julbouln/musicboard/firmware/src/bsp/musicboard/musicboard.c

/**
  ******************************************************************************
  * @file    stm32746g_discovery.c
  * @author  MCD Application Team
  * @version V1.0.0
  * @date    25-June-2015
  * @brief   This file provides a set of firmware functions to manage LEDs, 
  *          push-buttons and COM ports available on STM32746G-Discovery
  *          board(MB1191) from STMicroelectronics.
  ******************************************************************************
  * @attention
  *
  * <h2><center>&copy; COPYRIGHT(c) 2015 STMicroelectronics</center></h2>
  *
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
  ******************************************************************************
  */ 

/* Includes ------------------------------------------------------------------*/
#include "musicboard.h"

/** @addtogroup BSP
  * @{
  */ 

/** @addtogroup STM32746G_DISCOVERY
  * @{
  */

/** @defgroup STM32746G_DISCOVERY_LOW_LEVEL STM32746G_DISCOVERY_LOW_LEVEL
  * @{
  */

/** @defgroup STM32746G_DISCOVERY_LOW_LEVEL_Private_TypesDefinitions STM32746G_DISCOVERY_LOW_LEVEL Private Types Definitions
  * @{
  */
/**
  * @}
  */

/** @defgroup STM32746G_DISCOVERY_LOW_LEVEL_Private_Defines STM32746G_DISCOVERY_LOW_LEVEL Private Defines
  * @{
  */
/**
 * @brief STM32746G DISCOVERY BSP Driver version number V1.0.0
   */
#define __STM32746G_DISCO_BSP_VERSION_MAIN   (0x01) /*!< [31:24] main version */
#define __STM32746G_DISCO_BSP_VERSION_SUB1   (0x00) /*!< [23:16] sub1 version */
#define __STM32746G_DISCO_BSP_VERSION_SUB2   (0x00) /*!< [15:8]  sub2 version */
#define __STM32746G_DISCO_BSP_VERSION_RC     (0x00) /*!< [7:0]  release candidate */
#define __STM32746G_DISCO_BSP_VERSION         ((__STM32746G_DISCO_BSP_VERSION_MAIN << 24)\
                                             |(__STM32746G_DISCO_BSP_VERSION_SUB1 << 16)\
                                             |(__STM32746G_DISCO_BSP_VERSION_SUB2 << 8 )\
                                             |(__STM32746G_DISCO_BSP_VERSION_RC))
/**
  * @}
  */

/** @defgroup STM32746G_DISCOVERY_LOW_LEVEL_Private_Macros STM32746G_DISCOVERY_LOW_LEVEL Private Macros
  * @{
  */
/**
  * @}
  */

/** @defgroup STM32746G_DISCOVERY_LOW_LEVEL_Private_Variables STM32746G_DISCOVERY_LOW_LEVEL Private Variables
  * @{
  */

#ifdef LED2_PIN
const uint32_t GPIO_PIN[LEDn] = {LED1_PIN, LED2_PIN};
const GPIO_TypeDef* GPIO_PORT[LEDn] = {LED1_GPIO_PORT, LED2_GPIO_PORT};
#else
const uint32_t GPIO_PIN[LEDn] = {LED1_PIN};
const GPIO_TypeDef* GPIO_PORT[LEDn] = {LED1_GPIO_PORT};
#endif
USART_TypeDef* COM_USART[COMn] = {MIDI_COM1};
GPIO_TypeDef* COM_TX_PORT[COMn] = {MIDI_COM1_TX_GPIO_PORT};
GPIO_TypeDef* COM_RX_PORT[COMn] = {MIDI_COM1_RX_GPIO_PORT};
const uint16_t COM_TX_PIN[COMn] = {MIDI_COM1_TX_PIN};
const uint16_t COM_RX_PIN[COMn] = {MIDI_COM1_RX_PIN};
const uint16_t COM_TX_AF[COMn] = {MIDI_COM1_TX_AF};
const uint16_t COM_RX_AF[COMn] = {MIDI_COM1_RX_AF};

static I2C_HandleTypeDef hI2cAudioHandler = {0};

/**
  * @}
  */

/** @defgroup STM32746G_DISCOVERY_LOW_LEVEL_Private_FunctionPrototypes STM32746G_DISCOVERY_LOW_LEVEL Private Function Prototypes
  * @{
  */
static void     I2Cx_MspInit(I2C_HandleTypeDef *i2c_handler);
static void     I2Cx_Init(I2C_HandleTypeDef *i2c_handler);

/* AUDIO IO functions */
void            AUDIO_IO_Init(void);
void            AUDIO_IO_DeInit(void);
void            AUDIO_IO_Write(uint8_t Addr, uint16_t Reg, uint16_t Value);
uint16_t        AUDIO_IO_Read(uint8_t Addr, uint16_t Reg);
void            AUDIO_IO_Delay(uint32_t Delay);

/** @defgroup STM32746G_DISCOVERY_LOW_LEVEL_Exported_Functions STM32746G_DISCOVERY_LOW_LEVELSTM32746G_DISCOVERY_LOW_LEVEL Exported Functions
  * @{
  */ 

  /**
  * @brief  This method returns the STM32746G DISCOVERY BSP Driver revision
  * @retval version: 0xXYZR (8bits for each decimal, R for RC)
  */
uint32_t BSP_GetVersion(void)
{
  return __STM32746G_DISCO_BSP_VERSION;
}

/**
  * @brief  Configures LED on GPIO.
  * @param  Led: LED to be configured.
  *          This parameter can be one of the following values:
  *            @arg  LED1
  * @retval None
  */
void BSP_LED_Init(Led_TypeDef Led)
{
  GPIO_InitTypeDef  gpio_init_structure;
  GPIO_TypeDef*     gpio_led;

  gpio_led = GPIO_PORT[Led];
  /* Enable the GPIO_LED clock */
  if (Led == LED1)
  {
    LED1_GPIO_CLK_ENABLE();
  }
#ifdef LED2_PIN
  if (Led == LED2)
  {
    LED2_GPIO_CLK_ENABLE();
  }
#endif
  /* Configure the GPIO_LED pin */
  gpio_init_structure.Pin = GPIO_PIN[Led];
  gpio_init_structure.Mode = GPIO_MODE_OUTPUT_PP;
  gpio_init_structure.Pull = GPIO_PULLUP;
  gpio_init_structure.Speed = GPIO_SPEED_HIGH;

  HAL_GPIO_Init(gpio_led, &gpio_init_structure);

  /* By default, turn off LED */
  HAL_GPIO_WritePin(gpio_led, GPIO_PIN[Led], GPIO_PIN_RESET);
}

/**
  * @brief  DeInit LEDs.
  * @param  Led: LED to be configured.
  *          This parameter can be one of the following values:
  *            @arg  LED1
  * @note Led DeInit does not disable the GPIO clock
  * @retval None
  */
void BSP_LED_DeInit(Led_TypeDef Led)
{
  GPIO_InitTypeDef  gpio_init_structure;
  GPIO_TypeDef*     gpio_led;

  gpio_led = GPIO_PORT[Led];
  /* Turn off LED */
  HAL_GPIO_WritePin(gpio_led, GPIO_PIN[Led], GPIO_PIN_RESET);
  /* Configure the GPIO_LED pin */
  gpio_init_structure.Pin = GPIO_PIN[Led];
  HAL_GPIO_DeInit(gpio_led, gpio_init_structure.Pin);
}

/**
  * @brief  Turns selected LED On.
  * @param  Led: LED to be set on
  *          This parameter can be one of the following values:
  *            @arg  LED1
  * @retval None
  */
void BSP_LED_On(Led_TypeDef Led)
{
  GPIO_TypeDef*     gpio_led;

  gpio_led = GPIO_PORT[Led];
  HAL_GPIO_WritePin(gpio_led, GPIO_PIN[Led], GPIO_PIN_SET);
}

/**
  * @brief  Turns selected LED Off.
  * @param  Led: LED to be set off
  *          This parameter can be one of the following values:
  *            @arg  LED1
  * @retval None
  */
void BSP_LED_Off(Led_TypeDef Led)
{
  GPIO_TypeDef*     gpio_led;

  gpio_led = GPIO_PORT[Led];
  HAL_GPIO_WritePin(gpio_led, GPIO_PIN[Led], GPIO_PIN_RESET);
}

/**
  * @brief  Toggles the selected LED.
  * @param  Led: LED to be toggled
  *          This parameter can be one of the following values:
  *            @arg  LED1
  * @retval None
  */
void BSP_LED_Toggle(Led_TypeDef Led)
{
  GPIO_TypeDef*     gpio_led;

  gpio_led = GPIO_PORT[Led];
  HAL_GPIO_TogglePin(gpio_led, GPIO_PIN[Led]);
}

/**
  * @brief  Configures COM port.
  * @param  COM: COM port to be configured.
  *          This parameter can be one of the following values:
  *            @arg  COM1 
  *            @arg  COM2 
  * @param  huart: Pointer to a UART_HandleTypeDef structure that contains the
  *                configuration information for the specified USART peripheral.
  * @retval None
  */
void BSP_COM_Init(COM_TypeDef COM, UART_HandleTypeDef *huart)
{
  GPIO_InitTypeDef gpio_init_structure;

  /* Enable GPIO clock */
  MIDI_COMx_TX_GPIO_CLK_ENABLE(COM);
  MIDI_COMx_RX_GPIO_CLK_ENABLE(COM);

  /* Enable USART clock */
  MIDI_COMx_CLK_ENABLE(COM);

  /* Configure USART Tx as alternate function */
  gpio_init_structure.Pin = COM_TX_PIN[COM];
  gpio_init_structure.Mode = GPIO_MODE_AF_PP;
  gpio_init_structure.Speed = GPIO_SPEED_FAST;
  gpio_init_structure.Pull = GPIO_PULLUP;
  gpio_init_structure.Alternate = COM_TX_AF[COM];
  HAL_GPIO_Init(COM_TX_PORT[COM], &gpio_init_structure);

  /* Configure USART Rx as alternate function */
  gpio_init_structure.Pin = COM_RX_PIN[COM];
  gpio_init_structure.Mode = GPIO_MODE_AF_PP;
  gpio_init_structure.Alternate = COM_RX_AF[COM];
  HAL_GPIO_Init(COM_RX_PORT[COM], &gpio_init_structure);

  /* USART configuration */
  huart->Instance = COM_USART[COM];

  huart->Init.BaudRate = 31250;
  huart->Init.WordLength = UART_WORDLENGTH_8B;
  huart->Init.StopBits = UART_STOPBITS_1;
  huart->Init.Parity = UART_PARITY_NONE;
  huart->Init.Mode = UART_MODE_TX_RX;
  huart->Init.HwFlowCtl = UART_HWCONTROL_NONE;
  huart->Init.OverSampling = UART_OVERSAMPLING_16;
  huart->Init.OneBitSampling = UART_ONE_BIT_SAMPLE_DISABLE;
  huart->AdvancedInit.AdvFeatureInit = UART_ADVFEATURE_NO_INIT;

  HAL_UART_Init(huart);
}

/**
  * @brief  DeInit COM port.
  * @param  COM: COM port to be configured.
  *          This parameter can be one of the following values:
  *            @arg  COM1 
  *            @arg  COM2 
  * @param  huart: Pointer to a UART_HandleTypeDef structure that contains the
  *                configuration information for the specified USART peripheral.
  * @retval None
  */
void BSP_COM_DeInit(COM_TypeDef COM, UART_HandleTypeDef *huart)
{
  /* USART configuration */
  huart->Instance = COM_USART[COM];
  HAL_UART_DeInit(huart);

  /* Enable USART clock */
  MIDI_COMx_CLK_DISABLE(COM);

  /* DeInit GPIO pins can be done in the application 
     (by surcharging this __weak function) */

  /* GPIO pins clock, DMA clock can be shut down in the application 
     by surcharging this __weak function */
}

/*******************************************************************************
                            BUS OPERATIONS
*******************************************************************************/

/******************************* I2C Routines *********************************/
/**
  * @brief  Initializes I2C MSP.
  * @param  i2c_handler : I2C handler
  * @retval None
  */
static void I2Cx_MspInit(I2C_HandleTypeDef *i2c_handler)
{
  GPIO_InitTypeDef  gpio_init_structure;
  
  if (i2c_handler == (I2C_HandleTypeDef*)(&hI2cAudioHandler))
  {
    /* AUDIO MSP init */

    /* rev0 bug, set PB10 as input */
    gpio_init_structure.Pin = GPIO_PIN_10;
    gpio_init_structure.Mode = GPIO_MODE_INPUT;
    gpio_init_structure.Pull = GPIO_NOPULL;
    gpio_init_structure.Speed = GPIO_SPEED_FAST;
    HAL_GPIO_Init(GPIOB, &gpio_init_structure);

    /*** Configure the GPIOs ***/
    /* Enable GPIO clock */
    DISCOVERY_AUDIO_I2Cx_SCL_SDA_GPIO_CLK_ENABLE();

    /* Configure I2C Tx as alternate function */
    gpio_init_structure.Pin = DISCOVERY_AUDIO_I2Cx_SCL_PIN;
    gpio_init_structure.Mode = GPIO_MODE_AF_OD;
    gpio_init_structure.Pull = GPIO_NOPULL;
    gpio_init_structure.Speed = GPIO_SPEED_FAST;
    gpio_init_structure.Alternate = DISCOVERY_AUDIO_I2Cx_SCL_SDA_AF;
    HAL_GPIO_Init(DISCOVERY_AUDIO_I2Cx_SCL_SDA_GPIO_PORT, &gpio_init_structure);

    /* Configure I2C Rx as alternate function */
    gpio_init_structure.Pin = DISCOVERY_AUDIO_I2Cx_SDA_PIN;
    HAL_GPIO_Init(DISCOVERY_AUDIO_I2Cx_SCL_SDA_GPIO_PORT, &gpio_init_structure);

    /*** Configure the I2C peripheral ***/
    /* Enable I2C clock */
    DISCOVERY_AUDIO_I2Cx_CLK_ENABLE();

    /* Force the I2C peripheral clock reset */
    DISCOVERY_AUDIO_I2Cx_FORCE_RESET();

    /* Release the I2C peripheral clock reset */
    DISCOVERY_AUDIO_I2Cx_RELEASE_RESET();

    /* Enable and set I2Cx Interrupt to a lower priority */
    HAL_NVIC_SetPriority(DISCOVERY_AUDIO_I2Cx_EV_IRQn, 0x05, 0);
    HAL_NVIC_EnableIRQ(DISCOVERY_AUDIO_I2Cx_EV_IRQn);

    /* Enable and set I2Cx Interrupt to a lower priority */
    HAL_NVIC_SetPriority(DISCOVERY_AUDIO_I2Cx_ER_IRQn, 0x05, 0);
    HAL_NVIC_EnableIRQ(DISCOVERY_AUDIO_I2Cx_ER_IRQn);
  }
}

/**
  * @brief  Initializes I2C HAL.
  * @param  i2c_handler : I2C handler
  * @retval None
  */
static void I2Cx_Init(I2C_HandleTypeDef *i2c_handler)
{
  if(HAL_I2C_GetState(i2c_handler) == HAL_I2C_STATE_RESET)
  {
    if (i2c_handler == (I2C_HandleTypeDef*)(&hI2cAudioHandler))
    {
      /* Audio and LCD I2C configuration */
      i2c_handler->Instance = DISCOVERY_AUDIO_I2Cx;
    }

    i2c_handler->Init.Timing           = 0x10E66A8D; // generated by cubemx
    i2c_handler->Init.OwnAddress1      = 0;
    i2c_handler->Init.AddressingMode   = I2C_ADDRESSINGMODE_7BIT;
    i2c_handler->Init.DualAddressMode  = I2C_DUALADDRESS_DISABLE;
    i2c_handler->Init.OwnAddress2      = 0;
    i2c_handler->Init.GeneralCallMode  = I2C_GENERALCALL_DISABLE;
    i2c_handler->Init.NoStretchMode    = I2C_NOSTRETCH_DISABLE;

    /* Init the I2C */
    I2Cx_MspInit(i2c_handler);
    HAL_I2C_Init(i2c_handler);
  }
}

/*******************************************************************************
                            LINK OPERATIONS
*******************************************************************************/

/********************************* LINK AUDIO *********************************/

/**
  * @brief  Initializes Audio low level.
  * @retval None
  */
void AUDIO_IO_Init(void) 
{
  I2Cx_Init(&hI2cAudioHandler);
  //I2Cx_IsDeviceReady(&hI2cAudioHandler,AUDIO_I2C_ADDRESS,10);

}

/**
  * @brief  Deinitializes Audio low level.
  * @retval None
  */
void AUDIO_IO_DeInit(void)
{
}

/**
  * @brief  Writes a single data.
  * @param  Addr: I2C address
  * @param  Reg: Reg address 
  * @param  Value: Data to be written
  * @retval None
  */
void AUDIO_IO_Write(uint8_t Addr, uint16_t Reg, uint16_t Value)
{
  uint8_t cmd[2];
  /* Assemble 2-byte data in WM8731 format */
  cmd[0] = ((Reg << 1) & 0xFE) | ((Value >> 8) & 0x01);
  cmd[1] = Value & 0xFF;

  HAL_I2C_Master_Transmit(&hI2cAudioHandler, Addr, cmd, 2, 2000);  
}

/**
  * @brief  Reads a single data.
  * @param  Addr: I2C address
  * @param  Reg: Reg address 
  * @retval Data to be read
  */
uint16_t AUDIO_IO_Read(uint8_t Addr, uint16_t Reg)
{
  uint16_t read_value = 0;
  HAL_I2C_Master_Receive(&hI2cAudioHandler, Addr, (uint8_t*)&read_value, 2, 100);
  return read_value;
}

/**
  * @brief  AUDIO Codec delay 
  * @param  Delay: Delay in ms
  * @retval None
  */
void AUDIO_IO_Delay(uint32_t Delay)
{
  HAL_Delay(Delay);
}
