julbouln/musicboard/firmware/src/efluidsynth/fluid_voice.c

#include "fluid_voice.h"
#include "fluid_mod.h"
#include "fluid_chan.h"
#include "fluid_conv.h"
#include "fluid_synth.h"
#include "fluid_sys.h"
#include "fluid_sfont.h"
#include "fluid_log.h"

#include "fluid_types.h"

/* used for filter turn off optimization - if filter cutoff is above the
   specified value and filter q is below the other value, turn filter off */
#define FLUID_MAX_AUDIBLE_FILTER_FC 19000.0f
#define FLUID_MIN_AUDIBLE_FILTER_Q 1.2f

/* Smallest amplitude that can be perceived (full scale is +/- 0.5)
 * 16 bits => 96+4=100 dB dynamic range => 0.00001
 * 0.00001 * 2 is approximately 0.00003 :)
 */
#define FLUID_NOISE_FLOOR 0.00003

/* these should be the absolute minimum that FluidSynth can deal with */
#define FLUID_MIN_LOOP_SIZE 2
#define FLUID_MIN_LOOP_PAD 0

/* min vol envelope release (to stop clicks) in SoundFont timecents */
#define FLUID_MIN_VOLENVRELEASE -7200.0f /* ~16ms */

/*
 * new_fluid_voice
 */
fluid_voice_t*
new_fluid_voice(fluid_real_t output_rate)
{
  fluid_voice_t* voice;
  voice = FLUID_NEW(fluid_voice_t);
  if (voice == NULL) {
    FLUID_LOG(FLUID_ERR, "Out of memory");
    return NULL;
  }
  voice->status = FLUID_VOICE_CLEAN;
  voice->chan = NO_CHANNEL;
  voice->key = 0;
  voice->vel = 0;
  voice->channel = NULL;
  voice->sample = NULL;
  voice->output_rate = output_rate;

  /* The 'sustain' and 'finished' segments of the volume / modulation
   * envelope are constant. They are never affected by any modulator
   * or generator. Therefore it is enough to initialize them once
   * during the lifetime of the synth.
   */
  voice->volenv_data[FLUID_VOICE_ENVSUSTAIN].count = 0xffffffff;
  voice->volenv_data[FLUID_VOICE_ENVSUSTAIN].coeff = 1.0f;
  voice->volenv_data[FLUID_VOICE_ENVSUSTAIN].incr = 0.0f;
  voice->volenv_data[FLUID_VOICE_ENVSUSTAIN].min = -1.0f;
  voice->volenv_data[FLUID_VOICE_ENVSUSTAIN].max = 2.0f;

  voice->volenv_data[FLUID_VOICE_ENVFINISHED].count = 0xffffffff;
  voice->volenv_data[FLUID_VOICE_ENVFINISHED].coeff = 0.0f;
  voice->volenv_data[FLUID_VOICE_ENVFINISHED].incr = 0.0f;
  voice->volenv_data[FLUID_VOICE_ENVFINISHED].min = -1.0f;
  voice->volenv_data[FLUID_VOICE_ENVFINISHED].max = 1.0f;

  voice->modenv_data[FLUID_VOICE_ENVSUSTAIN].count = 0xffffffff;
  voice->modenv_data[FLUID_VOICE_ENVSUSTAIN].coeff = 1.0f;
  voice->modenv_data[FLUID_VOICE_ENVSUSTAIN].incr = 0.0f;
  voice->modenv_data[FLUID_VOICE_ENVSUSTAIN].min = -1.0f;
  voice->modenv_data[FLUID_VOICE_ENVSUSTAIN].max = 2.0f;

  voice->modenv_data[FLUID_VOICE_ENVFINISHED].count = 0xffffffff;
  voice->modenv_data[FLUID_VOICE_ENVFINISHED].coeff = 0.0f;
  voice->modenv_data[FLUID_VOICE_ENVFINISHED].incr = 0.0f;
  voice->modenv_data[FLUID_VOICE_ENVFINISHED].min = -1.0f;
  voice->modenv_data[FLUID_VOICE_ENVFINISHED].max = 1.0f;

  voice->gen = NULL;
  voice->mod = NULL;

  return voice;
}

int delete_fluid_voice(fluid_voice_t* voice)
{
  if (voice == NULL) {
    return FLUID_OK;
  }

  FLUID_FREE(voice);
  return FLUID_OK;
}

int fluid_voice_init(fluid_voice_t* voice, fluid_sample_t* sample,
                 fluid_channel_t* channel, int key, int vel, unsigned int id,
                 unsigned int start_time, fluid_real_t gain)
{
  /* Note: The voice parameters will be initialized later, when the
   * generators have been retrieved from the sound font. Here, only
   * the 'working memory' of the voice (position in envelopes, history
   * of IIR filters, position in sample etc) is initialized. */

  voice->id = id;
  voice->chan = fluid_channel_get_num(channel);
  voice->key = (uint8_t) key;
  voice->vel = (uint8_t) vel;
  voice->channel = channel;
  voice->mod_count = 0;
  voice->sample = sample;
  voice->start_time = start_time;
  voice->ticks = 0;
  voice->has_looped = 0; /* Will be set during voice_write when the 2nd loop point is reached */
  voice->last_fres = -1; /* The filter coefficients have to be calculated later in the DSP loop. */
  voice->filter_startup = 1; /* Set the filter immediately, don't fade between old and new settings */
  voice->interp_method = fluid_channel_get_interp_method(voice->channel);

  /* vol env initialization */
  voice->volenv_count = 0;
  voice->volenv_section = 0;
  voice->volenv_val = 0.0f;

#ifdef FLUID_FIXED_POINT
  voice->amp = 0;
#else
  voice->amp = 0.0f; /* The last value of the volume envelope, used to
                        calculate the volume increment during
                        processing */
#endif
  /* mod env initialization*/
  voice->modenv_count = 0;
  voice->modenv_section = 0;
  voice->modenv_val = 0.0f;

  voice->modlfo_val = 0.0;/* Fixme: Retrieve from any other existing
                             voice on this channel to keep LFOs in
                             unison? */

  voice->viblfo_val = 0.0f; /* Fixme: See mod lfo */

  /* Clear sample history in filter */
#ifdef FLUID_SIMPLE_IIR
  voice->vibrapos = 0;
  voice->vibraspeed = 0;
#else
  voice->hist1 = 0;
  voice->hist2 = 0;
#endif


  /* Set all the generators to their default value, according to SF
   * 2.01 section 8.1.3 (page 48). The value of NRPN messages are
   * copied from the channel to the voice's generators. The sound font
   * loader overwrites them. The generator values are later converted
   * into voice parameters in
   * fluid_voice_calculate_runtime_synthesis_parameters.  */
  fluid_list_t *pg;
  pg = voice->gen;
  while (pg != NULL) {
    fluid_gen_t *tmpgen = (fluid_gen_t *) pg->data;
    FLUID_FREE(tmpgen);
    pg->data = NULL;
    pg = fluid_list_next(pg);
  }
  delete_fluid_list(voice->gen);
  voice->gen = NULL;

  voice->synth_gain = gain;
  /* avoid division by zero later*/
  if (voice->synth_gain < 0.0000001) {
    voice->synth_gain = 0.0000001;
  }

  /* For a looped sample, this value will be overwritten as soon as the
   * loop parameters are initialized (they may depend on modulators).
   * This value can be kept, it is a worst-case estimate.
   */

  voice->amplitude_that_reaches_noise_floor_nonloop = FLUID_NOISE_FLOOR / voice->synth_gain;
  voice->amplitude_that_reaches_noise_floor_loop = FLUID_NOISE_FLOOR / voice->synth_gain;

  /* Increment the reference count of the sample to prevent the
     unloading of the soundfont while this voice is playing. */
  fluid_sample_incr_ref(voice->sample);

  fluid_list_t *p;
  p = voice->mod;
  while (p != NULL) {
    fluid_mod_t *tmpmod = (fluid_mod_t *) p->data;
    FLUID_FREE(tmpmod);
    p->data = NULL;
    p = fluid_list_next(p);
  }
  delete_fluid_list(voice->mod);
  voice->mod = NULL;

  return FLUID_OK;
}

extern fluid_gen_info_t fluid_gen_info[];

fluid_gen_t *fluid_voice_gen_get_or_add(fluid_voice_t *voice, uint8_t num) {
  fluid_gen_t *gen = fluid_gen_get(voice->gen, num);
  if (!gen) {
    gen = fluid_gen_create(num);
#ifndef FLUID_NO_NRPN_EXT
    gen->nrpn = fluid_channel_get_gen(voice->channel, num);
#endif
//        printf("%d %f\n",num,gen->nrpn);
    voice->gen = fluid_list_append(voice->gen, gen);
  }

  return gen;
}

fluid_real_t fluid_voice_gen_val_or_default(fluid_voice_t *voice, uint8_t num) {
  fluid_gen_t *gen = fluid_gen_get(voice->gen, num);
  if (gen)
    return gen->val;
  else
    return fluid_gen_info[num].def;
}

fluid_real_t fluid_voice_gen_val_all_or_default(fluid_voice_t *voice, uint8_t num) {
  fluid_gen_t *gen = fluid_gen_get(voice->gen, num);

#ifndef FLUID_NO_NRPN_EXT
  if (gen)
    return (gen->val + gen->mod + gen->nrpn);
  else
    return fluid_gen_info[num].def;
#else
  if (gen)
    return (gen->val + gen->mod);
  else
    return fluid_gen_info[num].def;
#endif
}

void fluid_voice_gen_set(fluid_voice_t* voice, int i, float val)
{
  fluid_gen_t *gen = fluid_voice_gen_get_or_add(voice, i);
  gen->val = val;
  gen->flags = GEN_SET;
}

void fluid_voice_gen_incr(fluid_voice_t* voice, int i, float val)
{
  fluid_gen_t *gen = fluid_voice_gen_get_or_add(voice, i);
  gen->val += val;
  gen->flags = GEN_SET;
}

float fluid_voice_gen_get(fluid_voice_t* voice, int num)
{
//  fluid_gen_t *gen = fluid_voice_gen_get_or_add(voice, num);
  return fluid_voice_gen_val_or_default(voice, num);
}

fluid_real_t fluid_voice_gen_value(fluid_voice_t* voice, int num)
{
  /* This is an extension to the SoundFont standard. More
   * documentation is available at the fluid_synth_set_gen2()
   * function. */

  fluid_gen_t *gen = fluid_voice_gen_get_or_add(voice, num);
#ifndef FLUID_NO_NRPN_EXT
  if (gen->flags == GEN_ABS_NRPN) {
    return gen->nrpn;

  } else {
    return (fluid_real_t) (gen->val + gen->mod + gen->nrpn);
  }
#else
  return (fluid_real_t) (gen->val + gen->mod);
#endif
}

int fluid_voice_calc_vol_mod_env(fluid_voice_t *voice) {
  fluid_env_data_t* env_data;
  fluid_real_t x;

  env_data = &voice->volenv_data[voice->volenv_section];

  /* skip to the next section of the envelope if necessary */
  while (voice->volenv_count >= env_data->count)
  {
    // If we're switching envelope stages from decay to sustain, force the value to be the end value of the previous stage
    if (env_data && voice->volenv_section == FLUID_VOICE_ENVDECAY)
      voice->volenv_val = env_data->min * env_data->coeff;

    env_data = &voice->volenv_data[++voice->volenv_section];
    voice->volenv_count = 0;
  }

  /* calculate the envelope value and check for valid range */
  x = env_data->coeff * voice->volenv_val + env_data->incr;
  if (x < env_data->min)
  {
    x = env_data->min;
    voice->volenv_section++;
    voice->volenv_count = 0;
  }
  else if (x > env_data->max)
  {
    x = env_data->max;
    voice->volenv_section++;
    voice->volenv_count = 0;
  }

  voice->volenv_val = x;
  voice->volenv_count++;

  if (voice->volenv_section == FLUID_VOICE_ENVFINISHED)
  {
    fluid_voice_off (voice);
    return 1;
  }

  env_data = &voice->modenv_data[voice->modenv_section];

  /* skip to the next section of the envelope if necessary */
  while (voice->modenv_count >= env_data->count)
  {
    env_data = &voice->modenv_data[++voice->modenv_section];
    voice->modenv_count = 0;
  }

  /* calculate the envelope value and check for valid range */
  x = env_data->coeff * voice->modenv_val + env_data->incr;

  if (x < env_data->min)
  {
    x = env_data->min;
    voice->modenv_section++;
    voice->modenv_count = 0;
  }
  else if (x > env_data->max)
  {
    x = env_data->max;
    voice->modenv_section++;
    voice->modenv_count = 0;
  }

  voice->modenv_val = x;
  voice->modenv_count++;
  return 0;
}

int fluid_voice_calc_lfo(fluid_voice_t *voice) {
  if (voice->ticks >= voice->modlfo_delay)
  {
    voice->modlfo_val += voice->modlfo_incr;

    if (voice->modlfo_val > 1.0)
    {
      voice->modlfo_incr = -voice->modlfo_incr;
      voice->modlfo_val = (fluid_real_t) 2.0 - voice->modlfo_val;
    }
    else if (voice->modlfo_val < -1.0)
    {
      voice->modlfo_incr = -voice->modlfo_incr;
      voice->modlfo_val = (fluid_real_t) - 2.0 - voice->modlfo_val;
    }
  }

  if (voice->ticks >= voice->viblfo_delay)
  {
    voice->viblfo_val += voice->viblfo_incr;

    if (voice->viblfo_val > (fluid_real_t) 1.0)
    {
      voice->viblfo_incr = -voice->viblfo_incr;
      voice->viblfo_val = (fluid_real_t) 2.0 - voice->viblfo_val;
    }
    else if (voice->viblfo_val < -1.0)
    {
      voice->viblfo_incr = -voice->viblfo_incr;
      voice->viblfo_val = (fluid_real_t) - 2.0 - voice->viblfo_val;
    }
  }
  return 0;
}

int fluid_voice_calc_amp(fluid_voice_t *voice) {
  fluid_real_t target_amp;

  if (voice->volenv_section == FLUID_VOICE_ENVDELAY)
    return 1;  /* The volume amplitude is in hold phase. No sound is produced. */

  if (voice->volenv_section == FLUID_VOICE_ENVATTACK)
  {
    /* the envelope is in the attack section: ramp linearly to max value.
     * A positive modlfo_to_vol should increase volume (negative attenuation).
     */
    target_amp = fluid_atten2amp (voice->attenuation)
                 * fluid_cb2amp (voice->modlfo_val * -voice->modlfo_to_vol)
                 * voice->volenv_val;
  }
  else
  {
    fluid_real_t amplitude_that_reaches_noise_floor;
    fluid_real_t amp_max;

    target_amp = fluid_atten2amp (voice->attenuation) * fluid_cb2amp (960.0f * (1.0f - voice->volenv_val) + voice->modlfo_val * -voice->modlfo_to_vol);

    /* We turn off a voice, if the volume has dropped low enough. */

    /* A voice can be turned off, when an estimate for the volume
     * (upper bound) falls below that volume, that will drop the
     * sample below the noise floor.
     */

    /* If the loop amplitude is known, we can use it if the voice loop is within
     * the sample loop
     */

    if (voice->has_looped)
      amplitude_that_reaches_noise_floor = voice->amplitude_that_reaches_noise_floor_loop;
    else
      amplitude_that_reaches_noise_floor = voice->amplitude_that_reaches_noise_floor_nonloop;

    /* voice->attenuation_min is a lower boundary for the attenuation
     * now and in the future (possibly 0 in the worst case).  Now the
     * amplitude of sample and volenv cannot exceed amp_max (since
     * volenv_val can only drop):
     */

    amp_max = fluid_atten2amp (voice->min_attenuation_cB) * voice->volenv_val;

    /* And if amp_max is already smaller than the known amplitude,
     * which will attenuate the sample below the noise floor, then we
     * can safely turn off the voice. Duh. */
    if (amp_max < amplitude_that_reaches_noise_floor)
    {
      fluid_voice_off (voice);
      return 1;
    }
  }

  /* Volume increment to go from voice->amp to target_amp in FLUID_BUFSIZE steps */
  voice->amp_incr = (FLUID_REAL_TO_FRAC16(target_amp) - voice->amp) / FLUID_BUFSIZE;

  /* no volume and not changing? - No need to process */
#ifdef FLUID_FIXED_POINT
  if ((voice->amp == 0) && (voice->amp_incr == 0))
    return 1;
#else
  if ((voice->amp == 0.0f) && (voice->amp_incr == 0.0f))
    return 1;
#endif
  /* Calculate the number of samples, that the DSP loop advances
   * through the original waveform with each step in the output
   * buffer. It is the ratio between the frequencies of original
   * waveform and output waveform.*/
  voice->phase_incr = (uint64_t)(fluid_ct2hz_real(voice->pitch + voice->modlfo_val * voice->modlfo_to_pitch
                                 + voice->viblfo_val * voice->viblfo_to_pitch
                                 + voice->modenv_val * voice->modenv_to_pitch) / voice->root_pitch * 4294967296.0f);

  /* if phase_incr is not advancing, set it to the minimum fraction value (prevent stuckage) */
  if (voice->phase_incr == 0) voice->phase_incr = 1;

  return 0;
}

#ifdef FLUID_SIMPLE_IIR
// just calculate frequency
int fluid_voice_iir_filter_calc(fluid_voice_t *voice) {
  fluid_real_t fres;

  /*************** resonant filter ******************/

  /* calculate the frequency of the resonant filter in Hz */
  fres = fluid_ct2hz(voice->fres
                     + voice->modlfo_val * voice->modlfo_to_fc
                     + voice->modenv_val * voice->modenv_to_fc);

  /* FIXME - Still potential for a click during turn on, can we interpolate
     between 20khz cutoff and 0 Q? */

  /* I removed the optimization of turning the filter off when the
   * resonance frequence is above the maximum frequency. Instead, the
   * filter frequency is set to a maximum of 0.45 times the sampling
   * rate. For a 44100 kHz sampling rate, this amounts to 19845
   * Hz. The reason is that there were problems with anti-aliasing when the
   * synthesizer was run at lower sampling rates. Thanks to Stephan
   * Tassart for pointing me to this bug. By turning the filter on and
   * clipping the maximum filter frequency at 0.45*srate, the filter
   * is used as an anti-aliasing filter. */

  if (fres > 0.45f * voice->output_rate)
    fres = 0.45f * voice->output_rate;
  else if (fres < 5)
    fres = 5;

  if ((FLUID_ABS(fres - voice->last_fres) > 0.01))
  {
    float amp = 1.0;
    float w = 2.0 * M_PI * fres / voice->output_rate; // Pole angle
    float q = 1.0 - w / (2.0 * (amp + 0.5 / (1.0 + w)) + w - 2.0); // Pole magnitude
    voice->r = q * q;
    voice->c = voice->r + 1.0 - 2.0 * FLUID_COS(w) * q;
  }

  voice->last_fres = fres;

}

// http://www.musicdsp.org/archive.php?classid=3#27
void fluid_voice_iir_filter_apply(fluid_voice_t *voice, int cnt) {
  float r = voice->r;
  float c = voice->c;
  fluid_buf_t *dsp_buf = voice->dsp_buf;

  float vibrapos = voice->vibrapos;
  float vibraspeed = voice->vibraspeed;

  fluid_buf_t in;
  int i;

  for (i = 0; i < cnt; i++)
  {
    in = dsp_buf[i];
    /* Accelerate vibra by signal-vibra, multiplied by lowpasscutoff */
    vibraspeed += (in - vibrapos) * c;

    /* Add velocity to vibra's position */
    vibrapos += vibraspeed;

    /* Attenuate/amplify vibra's velocity by resonance */
    vibraspeed *= r;

    dsp_buf[i] = vibrapos;
  }

  voice->vibrapos = vibrapos;
  voice->vibraspeed = vibraspeed;
}

#else

int fluid_voice_iir_filter_calc(fluid_voice_t *voice) {
  fluid_real_t fres;

  /*************** resonant filter ******************/

  /* calculate the frequency of the resonant filter in Hz */
  fres = fluid_ct2hz(voice->fres
                     + voice->modlfo_val * voice->modlfo_to_fc
                     + voice->modenv_val * voice->modenv_to_fc);

  /* FIXME - Still potential for a click during turn on, can we interpolate
     between 20khz cutoff and 0 Q? */

  /* I removed the optimization of turning the filter off when the
   * resonance frequence is above the maximum frequency. Instead, the
   * filter frequency is set to a maximum of 0.45 times the sampling
   * rate. For a 44100 kHz sampling rate, this amounts to 19845
   * Hz. The reason is that there were problems with anti-aliasing when the
   * synthesizer was run at lower sampling rates. Thanks to Stephan
   * Tassart for pointing me to this bug. By turning the filter on and
   * clipping the maximum filter frequency at 0.45*srate, the filter
   * is used as an anti-aliasing filter. */

  if (fres > 0.45f * voice->output_rate)
    fres = 0.45f * voice->output_rate;
  else if (fres < 5)
    fres = 5;

  /* if filter enabled and there is a significant frequency change.. */
  if ((FLUID_ABS(fres - voice->last_fres) > 0.01))
  {
    /* The filter coefficients have to be recalculated (filter
    * parameters have changed). Recalculation for various reasons is
    * forced by setting last_fres to -1.  The flag filter_startup
    * indicates, that the DSP loop runs for the first time, in this
    * case, the filter is set directly, instead of smoothly fading
    * between old and new settings.
    *
    * Those equations from Robert Bristow-Johnson's `Cookbook
    * formulae for audio EQ biquad filter coefficients', obtained
    * from Harmony-central.com / Computer / Programming. They are
    * the result of the bilinear transform on an analogue filter
    * prototype. To quote, `BLT frequency warping has been taken
    * into account for both significant frequency relocation and for
    * bandwidth readjustment'. */

    fluid_real_t omega = (fluid_real_t) (2.0 * M_PI * (fres / ((fluid_real_t) voice->output_rate)));
    fluid_real_t sin_coeff = (fluid_real_t) FLUID_SIN(omega);
    fluid_real_t cos_coeff = (fluid_real_t) FLUID_COS(omega);
    fluid_real_t alpha_coeff = sin_coeff / (2.0f * voice->q_lin);
    fluid_real_t a0_inv = 1.0f / (1.0f + alpha_coeff);

    /* Calculate the filter coefficients. All coefficients are
     * normalized by a0. Think of `a1' as `a1/a0'.
     *
     * Here a couple of multiplications are saved by reusing common expressions.
     * The original equations should be:
     *  voice->b0=(1.-cos_coeff)*a0_inv*0.5*voice->filter_gain;
     *  voice->b1=(1.-cos_coeff)*a0_inv*voice->filter_gain;
     *  voice->b2=(1.-cos_coeff)*a0_inv*0.5*voice->filter_gain; */

    fluid_real_t a1_temp = -2.0f * cos_coeff * a0_inv;
    fluid_real_t a2_temp = (1.0f - alpha_coeff) * a0_inv;
    fluid_real_t b1_temp = (1.0f - cos_coeff) * a0_inv * voice->filter_gain;
    /* both b0 -and- b2 */

    fluid_real_t b02_temp = b1_temp * 0.5f;

    if (voice->filter_startup)
    {
      /* The filter is calculated, because the voice was started up.
       * In this case set the filter coefficients without delay.
       */
      voice->a1 = FLUID_REAL_TO_FRAC(a1_temp);
      voice->a2 = FLUID_REAL_TO_FRAC(a2_temp);
      voice->b02 = FLUID_REAL_TO_FRAC(b02_temp);
      voice->b1 = FLUID_REAL_TO_FRAC(b1_temp);
      voice->filter_coeff_incr_count = 0;
      voice->filter_startup = 0;
    }
    else
    {
      /* The filter frequency is changed.  Calculate an increment
       * factor, so that the new setting is reached after one buffer
       * length. x_incr is added to the current value FLUID_BUFSIZE
       * times. The length is arbitrarily chosen. Longer than one
       * buffer will sacrifice some performance, though.  Note: If
       * the filter is still too 'grainy', then increase this number
       * at will.
       */

#define FILTER_TRANSITION_SAMPLES (FLUID_BUFSIZE)

      voice->a1_incr = (FLUID_REAL_TO_FRAC(a1_temp) - voice->a1) / FILTER_TRANSITION_SAMPLES;
      voice->a2_incr = (FLUID_REAL_TO_FRAC(a2_temp) - voice->a2) / FILTER_TRANSITION_SAMPLES;
      voice->b02_incr = (FLUID_REAL_TO_FRAC(b02_temp) - voice->b02) / FILTER_TRANSITION_SAMPLES;
      voice->b1_incr = (FLUID_REAL_TO_FRAC(b1_temp) - voice->b1) / FILTER_TRANSITION_SAMPLES;

      /* Have to add the increments filter_coeff_incr_count times. */
      voice->filter_coeff_incr_count = FILTER_TRANSITION_SAMPLES;
    }
    voice->last_fres = fres;
  }
}

void fluid_voice_iir_filter_apply(fluid_voice_t *voice, int count) {
  /* IIR filter sample history */
  fluid_buf_t dsp_hist1 = voice->hist1;
  fluid_buf_t dsp_hist2 = voice->hist2;

  /* IIR filter coefficients */
  fluid_buf_t dsp_a1 = voice->a1;
  fluid_buf_t dsp_a2 = voice->a2;
  fluid_buf_t dsp_b02 = voice->b02;
  fluid_buf_t dsp_b1 = voice->b1;
  fluid_buf16_t dsp_a1_incr = voice->a1_incr;
  fluid_buf16_t dsp_a2_incr = voice->a2_incr;
  fluid_buf16_t dsp_b02_incr = voice->b02_incr;
  fluid_buf16_t dsp_b1_incr = voice->b1_incr;
  int dsp_filter_coeff_incr_count = voice->filter_coeff_incr_count;
  fluid_buf_t dsp_centernode;

  fluid_buf_t *dsp_buf = voice->dsp_buf;
  int dsp_i;

  fluid_buf_t dsp_in, dsp_h1_a1, dsp_h2_a2, dsp_h1_b1, dsp_cn_h2, dsp_cn_b2;
  /* filter (implement the voice filter according to SoundFont standard) */

  /* Check for denormal number (too close to zero). */
//  if (FLUID_ABS(dsp_hist1) < 1e-20) dsp_hist1 = 0.0f;  /* FIXME JMG - Is this even needed? */

  if (FLUID_ABS(FLUID_FRAC_TO_REAL(dsp_hist1)) < 1e-20) dsp_hist1 = 0;  /* FIXME JMG - Is this even needed? */

  /* Two versions of the filter loop. One, while the filter is
  * changing towards its new setting. The other, if the filter
  * doesn't change.
  */

  if (dsp_filter_coeff_incr_count > 0)
  {
    /* Increment is added to each filter coefficient filter_coeff_incr_count times. */
    for (dsp_i = 0; dsp_i < count; dsp_i++)
    {
      dsp_in = dsp_buf[dsp_i];
      /* The filter is implemented in Direct-II form. */
      dsp_h1_a1 = FLUID_BUF_SAT32(FLUID_BUF_MULT32(dsp_a1, dsp_hist1));
      dsp_h2_a2 = FLUID_BUF_MULT32(dsp_a2, dsp_hist2);

      dsp_centernode = FLUID_BUF_SAT_SUB32(dsp_in, dsp_h1_a1);
      dsp_centernode = FLUID_BUF_SAT_SUB32(dsp_centernode, dsp_h2_a2);
      dsp_cn_h2 = FLUID_BUF_SAT_ADD32(dsp_centernode, dsp_hist2);
      dsp_cn_b2 = FLUID_BUF_MULT32(dsp_b02, dsp_cn_h2);
      dsp_h1_b1 = FLUID_BUF_MULT32(dsp_b1, dsp_hist1);
      dsp_buf[dsp_i] = FLUID_BUF_SAT_ADD32(dsp_cn_b2, dsp_h1_b1);
      dsp_hist2 = dsp_hist1;
      dsp_hist1 = dsp_centernode;

      if (dsp_filter_coeff_incr_count-- > 0)
      {
        dsp_a1 += dsp_a1_incr;
        dsp_a2 += dsp_a2_incr;
        dsp_b02 += dsp_b02_incr;
        dsp_b1 += dsp_b1_incr;
      }
    } /* for dsp_i */
  }
  else /* The filter parameters are constant.  This is duplicated to save time. */
  {
    for (dsp_i = 0; dsp_i < count; dsp_i++)
    { /* The filter is implemented in Direct-II form. */
      dsp_in = dsp_buf[dsp_i];
      /* The filter is implemented in Direct-II form. */
      dsp_h1_a1 = FLUID_BUF_SAT32(FLUID_BUF_MULT32(dsp_a1, dsp_hist1));
      dsp_h2_a2 = FLUID_BUF_MULT32(dsp_a2, dsp_hist2);

      dsp_centernode = FLUID_BUF_SAT_SUB32(dsp_in, dsp_h1_a1);
      dsp_centernode = FLUID_BUF_SAT_SUB32(dsp_centernode, dsp_h2_a2);
      dsp_cn_h2 = FLUID_BUF_SAT_ADD32(dsp_centernode, dsp_hist2);
      dsp_cn_b2 = FLUID_BUF_MULT32(dsp_b02, dsp_cn_h2);
      dsp_h1_b1 = FLUID_BUF_MULT32(dsp_b1, dsp_hist1);
      dsp_buf[dsp_i] = FLUID_BUF_SAT_ADD32(dsp_cn_b2, dsp_h1_b1);
      dsp_hist2 = dsp_hist1;
      dsp_hist1 = dsp_centernode;
    }
  }
  voice->hist1 = dsp_hist1;
  voice->hist2 = dsp_hist2;
  voice->a1 = dsp_a1;
  voice->a2 = dsp_a2;
  voice->b02 = dsp_b02;
  voice->b1 = dsp_b1;
  voice->filter_coeff_incr_count = dsp_filter_coeff_incr_count;
}
#endif
/* Purpose:
 *
 * - filters (applies a lowpass filter with variable cutoff frequency and quality factor)
 * - mixes the processed sample to left and right output using the pan setting
 * - sends the processed sample to chorus and reverb
 *
 * Variable description:
 * - dsp_data: Pointer to the original waveform data
 * - dsp_left_buf: The generated signal goes here, left channel
 * - dsp_right_buf: right channel
 * - dsp_reverb_buf: Send to reverb unit
 * - dsp_chorus_buf: Send to chorus unit
 * - dsp_a1: Coefficient for the filter
 * - dsp_a2: same
 * - dsp_b0: same
 * - dsp_b1: same
 * - dsp_b2: same
 * - voice holds the voice structure
 *
 * A couple of variables are used internally, their results are discarded:
 * - dsp_i: Index through the output buffer
 * - dsp_phase_fractional: The fractional part of dsp_phase
 * - dsp_coeff: A table of four coefficients, depending on the fractional phase.
 *              Used to interpolate between samples.
 * - dsp_process_buffer: Holds the processed signal between stages
 * - dsp_centernode: delay line for the IIR filter
 * - dsp_hist1: same
 * - dsp_hist2: same
 *
 */

fluid_real_t interp_coeff_linear[FLUID_INTERP_MAX][2];

#if 0
/* 4th order (cubic) interpolation table (4 coefficients centered on 2nd) */
static fluid_real_t interp_coeff[FLUID_INTERP_MAX][4];

/* 7th order interpolation (7 coefficients centered on 3rd) */
static fluid_real_t sinc_table7[FLUID_INTERP_MAX][7];


#define SINC_INTERP_ORDER 7 /* 7th order constant */

#endif

/* Initializes interpolation tables */
void fluid_dsp_float_config (void)
{
  int i, i2;
  fluid_real_t x, v;
  fluid_real_t i_shifted;

  /* Initialize the coefficients for the interpolation. The math comes
   * from a mail, posted by Olli Niemitalo to the music-dsp mailing
   * list (I found it in the music-dsp archives
   * http://www.smartelectronix.com/musicdsp/).  */

  for (i = 0; i < FLUID_INTERP_MAX; i++)
  {
    x = (fluid_real_t) i / (fluid_real_t) FLUID_INTERP_MAX;
    interp_coeff_linear[i][0] = (fluid_real_t)(1.0 - x);
    interp_coeff_linear[i][1] = (fluid_real_t)x;
  }

}

// TODO
int fluid_voice_calc_effects(fluid_voice_t *voice, fluid_buf_t* dsp_reverb_buf, fluid_buf_t* dsp_chorus_buf, uint16_t cnt)
{
  fluid_buf_t *dsp_buf = voice->dsp_buf;
  fluid_buf_t amp_reverb = FLUID_REAL_TO_FRAC16(voice->amp_reverb);
  fluid_buf_t amp_chorus = FLUID_REAL_TO_FRAC16(voice->amp_chorus);

  uint32_t dsp_cnt;
  fluid_buf_t in0, in1, in2, in3;

  if (dsp_reverb_buf != NULL) {
    dsp_cnt = (cnt >> 2);
    while (dsp_cnt > 0)
    {
      in0 = *(dsp_buf++);
      in1 = *(dsp_buf++);
      in2 = *(dsp_buf++);
      in3 = *(dsp_buf++);

      *(dsp_reverb_buf) = FLUID_BUF_MAC(amp_reverb, in0, *(dsp_reverb_buf));
      *(dsp_reverb_buf)++;
      *(dsp_reverb_buf) = FLUID_BUF_MAC(amp_reverb, in1, *(dsp_reverb_buf));
      *(dsp_reverb_buf)++;
      *(dsp_reverb_buf) = FLUID_BUF_MAC(amp_reverb, in2, *(dsp_reverb_buf));
      *(dsp_reverb_buf)++;
      *(dsp_reverb_buf) = FLUID_BUF_MAC(amp_reverb, in3, *(dsp_reverb_buf));
      *(dsp_reverb_buf)++;

      dsp_cnt--;
    }
  }

  dsp_buf = voice->dsp_buf;

  if (dsp_chorus_buf != NULL) {
    dsp_cnt = (cnt >> 2);
    while (dsp_cnt > 0)
    {
      in0 = *(dsp_buf++);
      in1 = *(dsp_buf++);
      in2 = *(dsp_buf++);
      in3 = *(dsp_buf++);

      *(dsp_chorus_buf) = FLUID_BUF_MAC(amp_chorus, in0, *(dsp_chorus_buf));
      *(dsp_chorus_buf)++;
      *(dsp_chorus_buf) = FLUID_BUF_MAC(amp_chorus, in1, *(dsp_chorus_buf));
      *(dsp_chorus_buf)++;
      *(dsp_chorus_buf) = FLUID_BUF_MAC(amp_chorus, in2, *(dsp_chorus_buf));
      *(dsp_chorus_buf)++;
      *(dsp_chorus_buf) = FLUID_BUF_MAC(amp_chorus, in3, *(dsp_chorus_buf));
      *(dsp_chorus_buf)++;

      dsp_cnt--;
    }
  }
  return cnt;
}

uint32_t fluid_voice_calc_stereo(fluid_voice_t *voice, fluid_buf_t* dsp_left_buf, fluid_buf_t* dsp_right_buf, uint32_t cnt)
{
  fluid_buf_t *dsp_buf = voice->dsp_buf;
  fluid_buf_t amp_left = FLUID_REAL_TO_FRAC16(voice->amp_left);
  fluid_buf_t amp_right = FLUID_REAL_TO_FRAC16(voice->amp_right);

  uint32_t dsp_cnt;
  fluid_buf_t in0, in1, in2, in3;

  dsp_cnt = (cnt >> 2);

  while (dsp_cnt > 0)
  {
    in0 = *(dsp_buf++);
    in1 = *(dsp_buf++);
    in2 = *(dsp_buf++);
    in3 = *(dsp_buf++);


    *(dsp_left_buf) = FLUID_BUF_MAC(amp_left, in0, *(dsp_left_buf));
    *(dsp_left_buf)++;
    *(dsp_left_buf) = FLUID_BUF_MAC(amp_left, in1, *(dsp_left_buf));
    *(dsp_left_buf)++;
    *(dsp_left_buf) = FLUID_BUF_MAC(amp_left, in2, *(dsp_left_buf));
    *(dsp_left_buf)++;
    *(dsp_left_buf) = FLUID_BUF_MAC(amp_left, in3, *(dsp_left_buf));
    *(dsp_left_buf)++;

    *(dsp_right_buf) = FLUID_BUF_MAC(amp_right, in0, *(dsp_right_buf));
    *(dsp_right_buf)++;
    *(dsp_right_buf) = FLUID_BUF_MAC(amp_right, in1, *(dsp_right_buf));
    *(dsp_right_buf)++;
    *(dsp_right_buf) = FLUID_BUF_MAC(amp_right, in2, *(dsp_right_buf));
    *(dsp_right_buf)++;
    *(dsp_right_buf) = FLUID_BUF_MAC(amp_right, in3, *(dsp_right_buf));
    *(dsp_right_buf)++;

    dsp_cnt--;
  } // 64 * 3 = 192 loop penalty (0.96us@200mhz)
  return cnt;
}

// one calculate function including interpolation and effects
uint32_t fluid_voice_interpolate(fluid_voice_t *voice)
{
  fluid_phase_t dsp_phase = voice->phase;
  fluid_phase_t dsp_phase_incr = voice->phase_incr;
  fluid_buf_t *dsp_buf = voice->dsp_buf;
  fluid_buf_t dsp_amp = voice->amp;
  fluid_buf_t dsp_amp_incr = voice->amp_incr;

  uint32_t dsp_cnt = 0;
  uint32_t dsp_phase_index;
  uint32_t end_index = voice->end_index;
  uint64_t loop_size = voice->loop_size;

  int16_t *buf = voice->sample->data;

  int32_t in0, in1, in2, in3;
  /*loop Unrolling */
  dsp_cnt = FLUID_BUFSIZE >> 2;
  dsp_phase_index = dsp_phase >> 32;

  while (dsp_cnt > 0)
  {
    in0 = FLUID_BUF_SAMPLE(*(buf + dsp_phase_index));
    dsp_phase += dsp_phase_incr;
    dsp_phase_index = dsp_phase >> 32;
    in1 = FLUID_BUF_SAMPLE(*(buf + dsp_phase_index));
    dsp_phase += dsp_phase_incr;
    dsp_phase_index = dsp_phase >> 32;
    in2 = FLUID_BUF_SAMPLE(*(buf + dsp_phase_index));
    dsp_phase += dsp_phase_incr;
    dsp_phase_index = dsp_phase >> 32;
    in3 = FLUID_BUF_SAMPLE(*(buf + dsp_phase_index));
    dsp_phase += dsp_phase_incr;
    dsp_phase_index = dsp_phase >> 32;

    dsp_amp += dsp_amp_incr;
    in0 = FLUID_BUF_MULT(dsp_amp, in0);
    dsp_amp += dsp_amp_incr;
    in1 = FLUID_BUF_MULT(dsp_amp, in1);
    dsp_amp += dsp_amp_incr;
    in2 = FLUID_BUF_MULT(dsp_amp, in2);
    dsp_amp += dsp_amp_incr;
    in3 = FLUID_BUF_MULT(dsp_amp, in3);

    *(dsp_buf++) = in0;
    *(dsp_buf++) = in1;
    *(dsp_buf++) = in2;
    *(dsp_buf++) = in3;

    if (dsp_phase_index > end_index)
    {
      if (voice->is_looping)
      {
        dsp_phase -= loop_size;
        voice->has_looped = 1;
        dsp_phase_index = dsp_phase >> 32;
      } else {
        break;
      }
    }

    dsp_cnt--;
  }

  voice->phase = dsp_phase;
  voice->amp = dsp_amp;
  return (FLUID_BUFSIZE - (dsp_cnt << 2));
}

/*
 * fluid_voice_write
 *
 * This is where it all happens. This function is called by the
 * synthesizer to generate the sound samples. The synthesizer passes
 * four audio buffers: left, right, reverb out, and chorus out.
 *
 * The biggest part of this function sets the correct values for all
 * the dsp parameters (all the control data boil down to only a few
 * dsp parameters). The dsp routine is #included in several places (fluid_dsp_core.c).
 */
int fluid_voice_write(fluid_voice_t* voice,
                  fluid_buf_t* dsp_left_buf, fluid_buf_t* dsp_right_buf,
                  fluid_buf_t* dsp_reverb_buf, fluid_buf_t* dsp_chorus_buf)
{
  if (voice->sample == NULL)
  {
    fluid_voice_off(voice);
    return FLUID_OK;
  }

  if (voice->sample->data == NULL) return FLUID_OK;

  if (!_PLAYING(voice)) return FLUID_OK;  /* make sure we're playing and that we have sample data */

  unsigned int i;
  fluid_real_t incr;
  uint32_t count;

  fluid_buf_t dsp_buf[FLUID_BUFSIZE];

  fluid_voice_check_sample_sanity (voice);

  if (fluid_voice_calc_vol_mod_env(voice))
    return FLUID_OK;

  fluid_voice_calc_lfo(voice);

  if (fluid_voice_calc_amp(voice)) {
    voice->ticks += FLUID_BUFSIZE;
    return FLUID_OK;
  }

  fluid_voice_iir_filter_calc(voice);

  voice->dsp_buf = dsp_buf;

  voice->is_looping = _SAMPLEMODE (voice) == FLUID_LOOP_DURING_RELEASE
                      || (_SAMPLEMODE (voice) == FLUID_LOOP_UNTIL_RELEASE
                          && voice->volenv_section < FLUID_VOICE_ENVRELEASE);


  if (voice->is_looping) {
    voice->end_index = voice->loopend;
    voice->loop_size = (uint64_t)(voice->loopend - voice->loopstart) << 32;
  }
  else {
    voice->end_index = voice->end;
    voice->loop_size = 0;
  }

  count = fluid_voice_interpolate(voice);

  fluid_voice_iir_filter_apply(voice, count);
  fluid_voice_calc_stereo(voice, dsp_left_buf, dsp_right_buf, count);
  fluid_voice_calc_effects(voice, dsp_reverb_buf, dsp_chorus_buf, count);

  /* turn off voice if short count (sample ended and not looping) */
  if (count < FLUID_BUFSIZE)
    fluid_voice_off(voice);

  voice->ticks += FLUID_BUFSIZE;
  return FLUID_OK;
}

fluid_channel_t* fluid_voice_get_channel(fluid_voice_t* voice)
{
  return voice->channel;
}

/*
 * fluid_voice_start
 */
void fluid_voice_start(fluid_voice_t* voice)
{
  /* The maximum volume of the loop is calculated and cached once for each
   * sample with its nominal loop settings. This happens, when the sample is used
   * for the first time.*/

  fluid_voice_calculate_runtime_synthesis_parameters(voice);

  /* Force setting of the phase at the first DSP loop run
   * This cannot be done earlier, because it depends on modulators.*/
  voice->check_sample_sanity_flag = FLUID_SAMPLESANITY_STARTUP;

  voice->status = FLUID_VOICE_ON;
}

/*
 * fluid_voice_calculate_runtime_synthesis_parameters
 *
 * in this function we calculate the values of all the parameters. the
 * parameters are converted to their most useful unit for the DSP
 * algorithm, for example, number of samples instead of
 * timecents. Some parameters keep their "perceptual" unit and
 * conversion will be done in the DSP function. This is the case, for
 * example, for the pitch since it is modulated by the controllers in
 * cents. */
int fluid_voice_calculate_runtime_synthesis_parameters(fluid_voice_t* voice)
{
  fluid_real_t x;
  fluid_real_t q_db;
  int i;

  int list_of_generators_to_initialize[35] = {
    GEN_STARTADDROFS,                    /* SF2.01 page 48 #0   */
    GEN_ENDADDROFS,                      /*                #1   */
    GEN_STARTLOOPADDROFS,                /*                #2   */
    GEN_ENDLOOPADDROFS,                  /*                #3   */
    /* GEN_STARTADDRCOARSEOFS see comment below [1]        #4   */
    GEN_MODLFOTOPITCH,                   /*                #5   */
    GEN_VIBLFOTOPITCH,                   /*                #6   */
    GEN_MODENVTOPITCH,                   /*                #7   */
    GEN_FILTERFC,                        /*                #8   */
    GEN_FILTERQ,                         /*                #9   */
    GEN_MODLFOTOFILTERFC,                /*                #10  */
    GEN_MODENVTOFILTERFC,                /*                #11  */
    /* GEN_ENDADDRCOARSEOFS [1]                            #12  */
    GEN_MODLFOTOVOL,                     /*                #13  */
    /* not defined                                         #14  */
    GEN_CHORUSSEND,                      /*                #15  */
    GEN_REVERBSEND,                      /*                #16  */
    GEN_PAN,                             /*                #17  */
    /* not defined                                         #18  */
    /* not defined                                         #19  */
    /* not defined                                         #20  */
    GEN_MODLFODELAY,                     /*                #21  */
    GEN_MODLFOFREQ,                      /*                #22  */
    GEN_VIBLFODELAY,                     /*                #23  */
    GEN_VIBLFOFREQ,                      /*                #24  */
    GEN_MODENVDELAY,                     /*                #25  */
    GEN_MODENVATTACK,                    /*                #26  */
    GEN_MODENVHOLD,                      /*                #27  */
    GEN_MODENVDECAY,                     /*                #28  */
    /* GEN_MODENVSUSTAIN [1]                               #29  */
    GEN_MODENVRELEASE,                   /*                #30  */
    /* GEN_KEYTOMODENVHOLD [1]                             #31  */
    /* GEN_KEYTOMODENVDECAY [1]                            #32  */
    GEN_VOLENVDELAY,                     /*                #33  */
    GEN_VOLENVATTACK,                    /*                #34  */
    GEN_VOLENVHOLD,                      /*                #35  */
    GEN_VOLENVDECAY,                     /*                #36  */
    /* GEN_VOLENVSUSTAIN [1]                               #37  */
    GEN_VOLENVRELEASE,                   /*                #38  */
    /* GEN_KEYTOVOLENVHOLD [1]                             #39  */
    /* GEN_KEYTOVOLENVDECAY [1]                            #40  */
    /* GEN_STARTLOOPADDRCOARSEOFS [1]                      #45  */
    GEN_KEYNUM,                          /*                #46  */
    GEN_VELOCITY,                        /*                #47  */
    GEN_ATTENUATION,                     /*                #48  */
    /* GEN_ENDLOOPADDRCOARSEOFS [1]                        #50  */
    /* GEN_COARSETUNE           [1]                        #51  */
    /* GEN_FINETUNE             [1]                        #52  */
    GEN_OVERRIDEROOTKEY,                 /*                #58  */
    GEN_PITCH,                           /*                ---  */
    -1
  };                                 /* end-of-list marker  */

  /* When the voice is made ready for the synthesis process, a lot of
   * voice-internal parameters have to be calculated.
   *
   * At this point, the sound font has already set the -nominal- value
   * for all generators (excluding GEN_PITCH). Most generators can be
   * modulated - they include a nominal value and an offset (which
   * changes with velocity, note number, channel parameters like
   * aftertouch, mod wheel...) Now this offset will be calculated as
   * follows:
   *
   *  - Process each modulator once.
   *  - Calculate its output value.
   *  - Find the target generator.
   *  - Add the output value to the modulation value of the generator.
   *
   * Note: The generators have been initialized with
   * fluid_gen_set_default_values.
   */

  fluid_list_t *p;
  p = voice->mod;
  while (p != NULL) {
    fluid_mod_t* mod = (fluid_mod_t *) p->data;
    fluid_real_t modval = fluid_mod_get_value(mod, voice->channel, voice);
    int dest_gen_index = mod->dest;
    fluid_gen_t* dest_gen = fluid_voice_gen_get_or_add(voice, dest_gen_index);

    dest_gen->mod += modval;
    p = fluid_list_next(p);
  }

  /* The GEN_PITCH is a hack to fit the pitch bend controller into the
   * modulator paradigm.  Now the nominal pitch of the key is set.
   * Note about SCALETUNE: SF2.01 8.1.3 says, that this generator is a
   * non-realtime parameter. So we don't allow modulation (as opposed
   * to _GEN(voice, GEN_SCALETUNE) When the scale tuning is varied,
   * one key remains fixed. Here C3 (MIDI number 60) is used.
   */
  if (fluid_channel_has_tuning(voice->channel)) {
    /* pitch(60) + scale * (pitch(key) - pitch(60)) */

    fluid_tuning_t* tuning = fluid_channel_get_tuning(voice->channel);

    fluid_gen_t* gen_pitch = fluid_voice_gen_get_or_add(voice, GEN_PITCH);
    fluid_real_t scaletune = fluid_voice_gen_val_or_default(voice, GEN_SCALETUNE);
    gen_pitch->val = (fluid_tuning_get_pitch(tuning, 60) + (scaletune / 100.0f *
                      (fluid_tuning_get_pitch(tuning, voice->key) - fluid_tuning_get_pitch(tuning, 60))));

  } else {
    fluid_gen_t* gen_pitch = fluid_voice_gen_get_or_add(voice, GEN_PITCH);
    fluid_real_t scaletune = fluid_voice_gen_val_or_default(voice, GEN_SCALETUNE);
    gen_pitch->val = (scaletune * (voice->key - 60.0f) + 100.0f * 60.0f);
  }

  /* Now the generators are initialized, nominal and modulation value.
   * The voice parameters (which depend on generators) are calculated
   * with fluid_voice_update_param. Processing the list of generator
   * changes will calculate each voice parameter once.
   *
   * Note [1]: Some voice parameters depend on several generators. For
   * example, the pitch depends on GEN_COARSETUNE, GEN_FINETUNE and
   * GEN_PITCH.  voice->pitch.  Unnecessary recalculation is avoided
   * by removing all but one generator from the list of voice
   * parameters.  Same with GEN_XXX and GEN_XXXCOARSE: the
   * initialisation list contains only GEN_XXX.
   */

  /* Calculate the voice parameter(s) dependent on each generator. */
  for (i = 0; list_of_generators_to_initialize[i] != -1; i++) {
    fluid_voice_update_param(voice, list_of_generators_to_initialize[i]);
  }

  /* Make an estimate on how loud this voice can get at any time (attenuation). */
  voice->min_attenuation_cB = fluid_voice_get_lower_boundary_for_attenuation(voice);

  return FLUID_OK;
}

/*
 * calculate_hold_decay_buffers
 */
int calculate_hold_decay_buffers(fluid_voice_t* voice, int gen_base,
                                 int gen_key2base, int is_decay)
{
  /* Purpose:
   *
   * Returns the number of DSP loops, that correspond to the hold
   * (is_decay=0) or decay (is_decay=1) time.
   * gen_base=GEN_VOLENVHOLD, GEN_VOLENVDECAY, GEN_MODENVHOLD,
   * GEN_MODENVDECAY gen_key2base=GEN_KEYTOVOLENVHOLD,
   * GEN_KEYTOVOLENVDECAY, GEN_KEYTOMODENVHOLD, GEN_KEYTOMODENVDECAY
   */

  fluid_real_t timecents;
  fluid_real_t seconds;
  int buffers;

  /* SF2.01 section 8.4.3 # 31, 32, 39, 40
   * GEN_KEYTOxxxENVxxx uses key 60 as 'origin'.
   * The unit of the generator is timecents per key number.
   * If KEYTOxxxENVxxx is 100, a key one octave over key 60 (72)
   * will cause (60-72)*100=-1200 timecents of time variation.
   * The time is cut in half.
   */
  timecents = (_GEN(voice, gen_base) + _GEN(voice, gen_key2base) * (60.0 - voice->key));

  /* Range checking */
  if (is_decay) {
    /* SF 2.01 section 8.1.3 # 28, 36 */
    if (timecents > 8000.0) {
      timecents = 8000.0;
    }
  } else {
    /* SF 2.01 section 8.1.3 # 27, 35 */
    if (timecents > 5000) {
      timecents = 5000.0;
    }
    /* SF 2.01 section 8.1.2 # 27, 35:
     * The most negative number indicates no hold time
     */
    if (timecents <= -32768.) {
      return 0;
    }
  }
  /* SF 2.01 section 8.1.3 # 27, 28, 35, 36 */
  if (timecents < -12000.0) {
    timecents = -12000.0;
  }

  seconds = fluid_tc2sec(timecents);
  /* Each DSP loop processes FLUID_BUFSIZE samples. */

  /* round to next full number of buffers */
  buffers = (int)(((fluid_real_t)voice->output_rate * seconds)
                  / (fluid_real_t)FLUID_BUFSIZE
                  + 0.5);

  return buffers;
}

/*
 * fluid_voice_update_param
 *
 * Purpose:
 *
 * The value of a generator (gen) has changed.  (The different
 * generators are listed in fluidsynth.h, or in SF2.01 page 48-49)
 * Now the dependent 'voice' parameters are calculated.
 *
 * fluid_voice_update_param can be called during the setup of the
 * voice (to calculate the initial value for a voice parameter), or
 * during its operation (a generator has been changed due to
 * real-time parameter modifications like pitch-bend).
 *
 * Note: The generator holds three values: The base value .val, an
 * offset caused by modulators .mod, and an offset caused by the
 * NRPN system. _GEN(voice, generator_enumerator) returns the sum
 * of all three.
 */
void fluid_voice_update_param(fluid_voice_t* voice, uint8_t gen)
{
  fluid_real_t q_dB;
  fluid_real_t x;
  fluid_real_t y;
  unsigned int count;
  // Alternate attenuation scale used by EMU10K1 cards when setting the attenuation at the preset or instrument level within the SoundFont bank.
  static const float ALT_ATTENUATION_SCALE = 0.4;

  switch (gen) {

  case GEN_PAN:
    /* range checking is done in the fluid_pan function */
    voice->pan = _GEN(voice, GEN_PAN);
    voice->amp_left = fluid_pan(voice->pan, 1) * voice->synth_gain;
#ifndef FLUID_FIXED_POINT
    voice->amp_left /= 32768.0f;
#endif

    voice->amp_right = fluid_pan(voice->pan, 0) * voice->synth_gain;
#ifndef FLUID_FIXED_POINT
    voice->amp_right /= 32768.0f;
#endif
    break;

  case GEN_ATTENUATION:
  {
    // TODO optimize
#ifndef FLUID_NO_NRPN_EXT
    fluid_gen_t *gen_att = fluid_voice_gen_get_or_add(voice, GEN_ATTENUATION);
    voice->attenuation = ((fluid_real_t)gen_att->val * ALT_ATTENUATION_SCALE) +
                         (fluid_real_t)gen_att->mod + (fluid_real_t)gen_att->nrpn;
#else
    fluid_gen_t *gen_att = fluid_voice_gen_get_or_add(voice, GEN_ATTENUATION);
    voice->attenuation = ((fluid_real_t)gen_att->val * ALT_ATTENUATION_SCALE) +
                         (fluid_real_t)gen_att->mod;

#endif
    /* Range: SF2.01 section 8.1.3 # 48
     * Motivation for range checking:
     * OHPiano.SF2 sets initial attenuation to a whooping -96 dB */
    fluid_clip(voice->attenuation, 0.0, 1440.0);
  }
  break;

  /* The pitch is calculated from three different generators.
   * Read comment in fluidsynth.h about GEN_PITCH.
   */
  case GEN_PITCH:
  case GEN_COARSETUNE:
  case GEN_FINETUNE:
    /* The testing for allowed range is done in 'fluid_ct2hz' */
    voice->pitch = (_GEN(voice, GEN_PITCH)
                    + 100.0f * _GEN(voice, GEN_COARSETUNE)
                    + _GEN(voice, GEN_FINETUNE));
    break;

  case GEN_REVERBSEND:
    /* The generator unit is 'tenths of a percent'. */
    voice->reverb_send = _GEN(voice, GEN_REVERBSEND) / 1000.0f;
    fluid_clip(voice->reverb_send, 0.0, 1.0);
    voice->amp_reverb = voice->reverb_send * voice->synth_gain;
#ifndef FLUID_FIXED_POINT
    voice->amp_reverb /= 32768.0f;
#endif

    break;

  case GEN_CHORUSSEND:
    /* The generator unit is 'tenths of a percent'. */
    voice->chorus_send = _GEN(voice, GEN_CHORUSSEND) / 1000.0f;
    fluid_clip(voice->chorus_send, 0.0, 1.0);
    voice->amp_chorus = voice->chorus_send * voice->synth_gain;
#ifndef FLUID_FIXED_POINT
    voice->amp_chorus /= 32768.0f;
#endif

    break;

  case GEN_OVERRIDEROOTKEY:
  {
    /* This is a non-realtime parameter. Therefore the .mod part of the generator
     * can be neglected.
     * NOTE: origpitch sets MIDI root note while pitchadj is a fine tuning amount
     * which offsets the original rate.  This means that the fine tuning is
     * inverted with respect to the root note (so subtract it, not add).
     */
    fluid_real_t ov = fluid_voice_gen_val_or_default(voice, GEN_OVERRIDEROOTKEY);
    if (ov > -1) {   //FIXME: use flag instead of -1
      voice->root_pitch = ov * 100.0f
                          - voice->sample->pitchadj;
    }
    else {
      voice->root_pitch = voice->sample->origpitch * 100.0f - voice->sample->pitchadj;
    }
    voice->root_pitch = fluid_ct2hz(voice->root_pitch);
    if (voice->sample != NULL) {
      voice->root_pitch *= (fluid_real_t) voice->output_rate / voice->sample->samplerate;
    }
  }
  break;

  case GEN_FILTERFC:
    /* The resonance frequency is converted from absolute cents to
     * midicents .val and .mod are both used, this permits real-time
     * modulation.  The allowed range is tested in the 'fluid_ct2hz'
     * function [PH,20021214]
     */
    voice->fres = _GEN(voice, GEN_FILTERFC);

    /* The synthesis loop will have to recalculate the filter
     * coefficients. */
    voice->last_fres = -1.0f;
    break;

  case GEN_FILTERQ:
    /* The generator contains 'centibels' (1/10 dB) => divide by 10 to
     * obtain dB */
    q_dB = _GEN(voice, GEN_FILTERQ) / 10.0f;

    /* Range: SF2.01 section 8.1.3 # 8 (convert from cB to dB => /10) */
    fluid_clip(q_dB, 0.0f, 96.0f);

    /* Short version: Modify the Q definition in a way, that a Q of 0
     * dB leads to no resonance hump in the freq. response.
     *
     * Long version: From SF2.01, page 39, item 9 (initialFilterQ):
     * "The gain at the cutoff frequency may be less than zero when
     * zero is specified".  Assume q_dB=0 / q_lin=1: If we would leave
     * q as it is, then this results in a 3 dB hump slightly below
     * fc. At fc, the gain is exactly the DC gain (0 dB).  What is
     * (probably) meant here is that the filter does not show a
     * resonance hump for q_dB=0. In this case, the corresponding
     * q_lin is 1/sqrt(2)=0.707.  The filter should have 3 dB of
     * attenuation at fc now.  In this case Q_dB is the height of the
     * resonance peak not over the DC gain, but over the frequency
     * response of a non-resonant filter.  This idea is implemented as
     * follows: */
    q_dB -= 3.01f;

    /* The 'sound font' Q is defined in dB. The filter needs a linear
       q. Convert. */
    voice->q_lin = (fluid_real_t) (FLUID_POW(10.0f, q_dB / 20.0f));

    /* SF 2.01 page 59:
     *
     *  The SoundFont specs ask for a gain reduction equal to half the
     *  height of the resonance peak (Q).  For example, for a 10 dB
     *  resonance peak, the gain is reduced by 5 dB.  This is done by
     *  multiplying the total gain with sqrt(1/Q).  `Sqrt' divides dB
     *  by 2 (100 lin = 40 dB, 10 lin = 20 dB, 3.16 lin = 10 dB etc)
     *  The gain is later factored into the 'b' coefficients
     *  (numerator of the filter equation).  This gain factor depends
     *  only on Q, so this is the right place to calculate it.
     */
    voice->filter_gain = (fluid_real_t) (1.0 / FLUID_SQRT(voice->q_lin));

    /* The synthesis loop will have to recalculate the filter coefficients. */
    voice->last_fres = -1.;
    break;

  case GEN_MODLFOTOPITCH:
    voice->modlfo_to_pitch = _GEN(voice, GEN_MODLFOTOPITCH);
    fluid_clip(voice->modlfo_to_pitch, -12000.0, 12000.0);
    break;

  case GEN_MODLFOTOVOL:
    voice->modlfo_to_vol = _GEN(voice, GEN_MODLFOTOVOL);
    fluid_clip(voice->modlfo_to_vol, -960.0, 960.0);
    break;

  case GEN_MODLFOTOFILTERFC:
    voice->modlfo_to_fc = _GEN(voice, GEN_MODLFOTOFILTERFC);
    fluid_clip(voice->modlfo_to_fc, -12000, 12000);
    break;

  case GEN_MODLFODELAY:
    x = _GEN(voice, GEN_MODLFODELAY);
    fluid_clip(x, -12000.0f, 5000.0f);
    voice->modlfo_delay = (unsigned int) (voice->output_rate * fluid_tc2sec_delay(x));
    break;

  case GEN_MODLFOFREQ:
    /* - the frequency is converted into a delta value, per buffer of FLUID_BUFSIZE samples
     * - the delay into a sample delay
     */
    x = _GEN(voice, GEN_MODLFOFREQ);
    fluid_clip(x, -16000.0f, 4500.0f);
    voice->modlfo_incr = (4.0f * FLUID_BUFSIZE * fluid_act2hz(x) / voice->output_rate);
    break;

  case GEN_VIBLFOFREQ:
    /* vib lfo
     *
     * - the frequency is converted into a delta value, per buffer of FLUID_BUFSIZE samples
     * - the delay into a sample delay
     */
    x = _GEN(voice, GEN_VIBLFOFREQ);
    fluid_clip(x, -16000.0f, 4500.0f);
    voice->viblfo_incr = (4.0f * FLUID_BUFSIZE * fluid_act2hz(x) / voice->output_rate);
    break;

  case GEN_VIBLFODELAY:
    x = _GEN(voice, GEN_VIBLFODELAY);
    fluid_clip(x, -12000.0f, 5000.0f);
    voice->viblfo_delay = (unsigned int) (voice->output_rate * fluid_tc2sec_delay(x));
    break;

  case GEN_VIBLFOTOPITCH:
    voice->viblfo_to_pitch = _GEN(voice, GEN_VIBLFOTOPITCH);
    fluid_clip(voice->viblfo_to_pitch, -12000.0, 12000.0);
    break;

  case GEN_KEYNUM:
    /* GEN_KEYNUM: SF2.01 page 46, item 46
     *
     * If this generator is active, it forces the key number to its
     * value.  Non-realtime controller.
     *
     * There is a flag, which should indicate, whether a generator is
     * enabled or not.  But here we rely on the default value of -1.
     * */
    x = _GEN(voice, GEN_KEYNUM);
    if (x >= 0) {
      voice->key = x;
    }
    break;

  case GEN_VELOCITY:
    /* GEN_VELOCITY: SF2.01 page 46, item 47
     *
     * If this generator is active, it forces the velocity to its
     * value. Non-realtime controller.
     *
     * There is a flag, which should indicate, whether a generator is
     * enabled or not. But here we rely on the default value of -1.  */
    x = _GEN(voice, GEN_VELOCITY);
    if (x > 0) {
      voice->vel = x;
    }
    break;

  case GEN_MODENVTOPITCH:
    voice->modenv_to_pitch = _GEN(voice, GEN_MODENVTOPITCH);
    fluid_clip(voice->modenv_to_pitch, -12000.0, 12000.0);
    break;

  case GEN_MODENVTOFILTERFC:
    voice->modenv_to_fc = _GEN(voice, GEN_MODENVTOFILTERFC);

    /* Range: SF2.01 section 8.1.3 # 1
     * Motivation for range checking:
     * Filter is reported to make funny noises now and then
     */
    fluid_clip(voice->modenv_to_fc, -12000.0, 12000.0);
    break;


  /* sample start and ends points
   *
   * Range checking is initiated via the
   * voice->check_sample_sanity flag,
   * because it is impossible to check here:
   * During the voice setup, all modulators are processed, while
   * the voice is inactive. Therefore, illegal settings may
   * occur during the setup (for example: First move the loop
   * end point ahead of the loop start point => invalid, then
   * move the loop start point forward => valid again.
   */
  case GEN_STARTADDROFS:              /* SF2.01 section 8.1.3 # 0 */
  case GEN_STARTADDRCOARSEOFS:        /* SF2.01 section 8.1.3 # 4 */
    if (voice->sample != NULL) {
      voice->start = (voice->sample->start
                      + (int) _GEN(voice, GEN_STARTADDROFS)
                      + 32768 * (int) _GEN(voice, GEN_STARTADDRCOARSEOFS));
      voice->check_sample_sanity_flag = FLUID_SAMPLESANITY_CHECK;
    }
    break;
  case GEN_ENDADDROFS:                 /* SF2.01 section 8.1.3 # 1 */
  case GEN_ENDADDRCOARSEOFS:           /* SF2.01 section 8.1.3 # 12 */
    if (voice->sample != NULL) {
      voice->end = (voice->sample->end
                    + (int) _GEN(voice, GEN_ENDADDROFS)
                    + 32768 * (int) _GEN(voice, GEN_ENDADDRCOARSEOFS));
      voice->check_sample_sanity_flag = FLUID_SAMPLESANITY_CHECK;
    }
    break;
  case GEN_STARTLOOPADDROFS:           /* SF2.01 section 8.1.3 # 2 */
  case GEN_STARTLOOPADDRCOARSEOFS:     /* SF2.01 section 8.1.3 # 45 */
    if (voice->sample != NULL) {
      voice->loopstart = (voice->sample->loopstart
                          + (int) _GEN(voice, GEN_STARTLOOPADDROFS)
                          + 32768 * (int) _GEN(voice, GEN_STARTLOOPADDRCOARSEOFS));
      voice->check_sample_sanity_flag = FLUID_SAMPLESANITY_CHECK;
    }
    break;

  case GEN_ENDLOOPADDROFS:             /* SF2.01 section 8.1.3 # 3 */
  case GEN_ENDLOOPADDRCOARSEOFS:       /* SF2.01 section 8.1.3 # 50 */
    if (voice->sample != NULL) {
      voice->loopend = (voice->sample->loopend
                        + (int) _GEN(voice, GEN_ENDLOOPADDROFS)
                        + 32768 * (int) _GEN(voice, GEN_ENDLOOPADDRCOARSEOFS));
      voice->check_sample_sanity_flag = FLUID_SAMPLESANITY_CHECK;
    }
    break;

    /* Conversion functions differ in range limit */
#define NUM_BUFFERS_DELAY(_v)   (unsigned int) (voice->output_rate * fluid_tc2sec_delay(_v) / FLUID_BUFSIZE)
#define NUM_BUFFERS_ATTACK(_v)  (unsigned int) (voice->output_rate * fluid_tc2sec_attack(_v) / FLUID_BUFSIZE)
#define NUM_BUFFERS_RELEASE(_v) (unsigned int) (voice->output_rate * fluid_tc2sec_release(_v) / FLUID_BUFSIZE)

  /* volume envelope
   *
   * - delay and hold times are converted to absolute number of samples
   * - sustain is converted to its absolute value
   * - attack, decay and release are converted to their increment per sample
   */
  case GEN_VOLENVDELAY:                /* SF2.01 section 8.1.3 # 33 */
    x = _GEN(voice, GEN_VOLENVDELAY);
    fluid_clip(x, -12000.0f, 5000.0f);
    count = NUM_BUFFERS_DELAY(x);
    voice->volenv_data[FLUID_VOICE_ENVDELAY].count = count;
    voice->volenv_data[FLUID_VOICE_ENVDELAY].coeff = 0.0f;
    voice->volenv_data[FLUID_VOICE_ENVDELAY].incr = 0.0f;
    voice->volenv_data[FLUID_VOICE_ENVDELAY].min = -1.0f;
    voice->volenv_data[FLUID_VOICE_ENVDELAY].max = 1.0f;
    break;

  case GEN_VOLENVATTACK:               /* SF2.01 section 8.1.3 # 34 */
    x = _GEN(voice, GEN_VOLENVATTACK);
    fluid_clip(x, -12000.0f, 8000.0f);
    count = 1 + NUM_BUFFERS_ATTACK(x);
    voice->volenv_data[FLUID_VOICE_ENVATTACK].count = count;
    voice->volenv_data[FLUID_VOICE_ENVATTACK].coeff = 1.0f;
    voice->volenv_data[FLUID_VOICE_ENVATTACK].incr = count ? 1.0f / count : 0.0f;
    voice->volenv_data[FLUID_VOICE_ENVATTACK].min = -1.0f;
    voice->volenv_data[FLUID_VOICE_ENVATTACK].max = 1.0f;
    break;

  case GEN_VOLENVHOLD:                 /* SF2.01 section 8.1.3 # 35 */
  case GEN_KEYTOVOLENVHOLD:            /* SF2.01 section 8.1.3 # 39 */
    count = calculate_hold_decay_buffers(voice, GEN_VOLENVHOLD, GEN_KEYTOVOLENVHOLD, 0); /* 0 means: hold */
    voice->volenv_data[FLUID_VOICE_ENVHOLD].count = count;
    voice->volenv_data[FLUID_VOICE_ENVHOLD].coeff = 1.0f;
    voice->volenv_data[FLUID_VOICE_ENVHOLD].incr = 0.0f;
    voice->volenv_data[FLUID_VOICE_ENVHOLD].min = -1.0f;
    voice->volenv_data[FLUID_VOICE_ENVHOLD].max = 2.0f;
    break;

  case GEN_VOLENVDECAY:               /* SF2.01 section 8.1.3 # 36 */
  case GEN_VOLENVSUSTAIN:             /* SF2.01 section 8.1.3 # 37 */
  case GEN_KEYTOVOLENVDECAY:          /* SF2.01 section 8.1.3 # 40 */
    y = 1.0f - 0.001f * _GEN(voice, GEN_VOLENVSUSTAIN);
    fluid_clip(y, 0.0f, 1.0f);
    count = calculate_hold_decay_buffers(voice, GEN_VOLENVDECAY, GEN_KEYTOVOLENVDECAY, 1); /* 1 for decay */
    voice->volenv_data[FLUID_VOICE_ENVDECAY].count = count;
    voice->volenv_data[FLUID_VOICE_ENVDECAY].coeff = 1.0f;
    voice->volenv_data[FLUID_VOICE_ENVDECAY].incr = count ? -1.0f / count : 0.0f;
    voice->volenv_data[FLUID_VOICE_ENVDECAY].min = y;
    voice->volenv_data[FLUID_VOICE_ENVDECAY].max = 2.0f;
    break;

  case GEN_VOLENVRELEASE:             /* SF2.01 section 8.1.3 # 38 */
    x = _GEN(voice, GEN_VOLENVRELEASE);
    fluid_clip(x, FLUID_MIN_VOLENVRELEASE, 8000.0f);
    count = 1 + NUM_BUFFERS_RELEASE(x);
    voice->volenv_data[FLUID_VOICE_ENVRELEASE].count = count;
    voice->volenv_data[FLUID_VOICE_ENVRELEASE].coeff = 1.0f;
    voice->volenv_data[FLUID_VOICE_ENVRELEASE].incr = count ? -1.0f / count : 0.0f;
    voice->volenv_data[FLUID_VOICE_ENVRELEASE].min = 0.0f;
    voice->volenv_data[FLUID_VOICE_ENVRELEASE].max = 1.0f;
    break;

  /* Modulation envelope */
  case GEN_MODENVDELAY:               /* SF2.01 section 8.1.3 # 25 */
    x = _GEN(voice, GEN_MODENVDELAY);
    fluid_clip(x, -12000.0f, 5000.0f);
    voice->modenv_data[FLUID_VOICE_ENVDELAY].count = NUM_BUFFERS_DELAY(x);
    voice->modenv_data[FLUID_VOICE_ENVDELAY].coeff = 0.0f;
    voice->modenv_data[FLUID_VOICE_ENVDELAY].incr = 0.0f;
    voice->modenv_data[FLUID_VOICE_ENVDELAY].min = -1.0f;
    voice->modenv_data[FLUID_VOICE_ENVDELAY].max = 1.0f;
    break;

  case GEN_MODENVATTACK:               /* SF2.01 section 8.1.3 # 26 */
    x = _GEN(voice, GEN_MODENVATTACK);
    fluid_clip(x, -12000.0f, 8000.0f);
    count = 1 + NUM_BUFFERS_ATTACK(x);
    voice->modenv_data[FLUID_VOICE_ENVATTACK].count = count;
    voice->modenv_data[FLUID_VOICE_ENVATTACK].coeff = 1.0f;
    voice->modenv_data[FLUID_VOICE_ENVATTACK].incr = count ? 1.0f / count : 0.0f;
    voice->modenv_data[FLUID_VOICE_ENVATTACK].min = -1.0f;
    voice->modenv_data[FLUID_VOICE_ENVATTACK].max = 1.0f;
    break;

  case GEN_MODENVHOLD:               /* SF2.01 section 8.1.3 # 27 */
  case GEN_KEYTOMODENVHOLD:          /* SF2.01 section 8.1.3 # 31 */
    count = calculate_hold_decay_buffers(voice, GEN_MODENVHOLD, GEN_KEYTOMODENVHOLD, 0); /* 1 means: hold */
    voice->modenv_data[FLUID_VOICE_ENVHOLD].count = count;
    voice->modenv_data[FLUID_VOICE_ENVHOLD].coeff = 1.0f;
    voice->modenv_data[FLUID_VOICE_ENVHOLD].incr = 0.0f;
    voice->modenv_data[FLUID_VOICE_ENVHOLD].min = -1.0f;
    voice->modenv_data[FLUID_VOICE_ENVHOLD].max = 2.0f;
    break;

  case GEN_MODENVDECAY:                                   /* SF 2.01 section 8.1.3 # 28 */
  case GEN_MODENVSUSTAIN:                                 /* SF 2.01 section 8.1.3 # 29 */
  case GEN_KEYTOMODENVDECAY:                              /* SF 2.01 section 8.1.3 # 32 */
    count = calculate_hold_decay_buffers(voice, GEN_MODENVDECAY, GEN_KEYTOMODENVDECAY, 1); /* 1 for decay */
    y = 1.0f - 0.001f * _GEN(voice, GEN_MODENVSUSTAIN);
    fluid_clip(y, 0.0f, 1.0f);
    voice->modenv_data[FLUID_VOICE_ENVDECAY].count = count;
    voice->modenv_data[FLUID_VOICE_ENVDECAY].coeff = 1.0f;
    voice->modenv_data[FLUID_VOICE_ENVDECAY].incr = count ? -1.0f / count : 0.0f;
    voice->modenv_data[FLUID_VOICE_ENVDECAY].min = y;
    voice->modenv_data[FLUID_VOICE_ENVDECAY].max = 2.0f;
    break;

  case GEN_MODENVRELEASE:                                  /* SF 2.01 section 8.1.3 # 30 */
    x = _GEN(voice, GEN_MODENVRELEASE);
    fluid_clip(x, -12000.0f, 8000.0f);
    count = 1 + NUM_BUFFERS_RELEASE(x);
    voice->modenv_data[FLUID_VOICE_ENVRELEASE].count = count;
    voice->modenv_data[FLUID_VOICE_ENVRELEASE].coeff = 1.0f;
    voice->modenv_data[FLUID_VOICE_ENVRELEASE].incr = count ? -1.0f / count : 0.0;
    voice->modenv_data[FLUID_VOICE_ENVRELEASE].min = 0.0f;
    voice->modenv_data[FLUID_VOICE_ENVRELEASE].max = 2.0f;
    break;

  } /* switch gen */
}
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
