julbouln/musicboard/firmware/src/efluidsynth/fluid_voice.h

#ifndef _FLUID_VOICE_H
#define _FLUID_VOICE_H

#include "fluid_phase.h"
#include "fluid_gen.h"
#include "fluid_mod.h"

#define NO_CHANNEL             0xff

enum fluid_voice_status
{
	FLUID_VOICE_CLEAN,
	FLUID_VOICE_ON,
	FLUID_VOICE_SUSTAINED,
	FLUID_VOICE_OFF
};

/*
 * envelope data
 */
struct _fluid_env_data_t {
	uint32_t count;
	fluid_real_t coeff;
	fluid_real_t incr;
	fluid_real_t min;
	fluid_real_t max;
};

/* Indices for envelope tables */
enum fluid_voice_envelope_index_t {
	FLUID_VOICE_ENVDELAY,
	FLUID_VOICE_ENVATTACK,
	FLUID_VOICE_ENVHOLD,
	FLUID_VOICE_ENVDECAY,
	FLUID_VOICE_ENVSUSTAIN,
	FLUID_VOICE_ENVRELEASE,
	FLUID_VOICE_ENVFINISHED,
	FLUID_VOICE_ENVLAST
};

/*
 * fluid_voice_t
 */
struct _fluid_voice_t
{
	uint32_t id;                /* the id is incremented for every new noteon.
					   it's used for noteoff's  */
	uint8_t status;
	uint8_t chan;             /* the channel number, quick access for channel messages */
	uint8_t key;              /* the key, quick acces for noteoff */
	uint8_t vel;              /* the velocity */
	fluid_channel_t* channel;
	fluid_list_t *gen;
	fluid_list_t *mod;
	uint8_t mod_count;
	uint8_t has_looped;                 /* Flag that is set as soon as the first loop is completed. */
	fluid_sample_t* sample;

	uint8_t check_sample_sanity_flag;   /* Flag that initiates, that sample-related parameters
					   have to be checked. */

	/* basic parameters */
	fluid_real_t output_rate;        /* the sample rate of the synthesizer */

	uint32_t start_time;
	uint32_t ticks;

	fluid_buf_t amp;                /* current linear amplitude */
	fluid_phase_t phase;             /* the phase of the sample wave */

	/* Temporary variables used in fluid_voice_write() */

	fluid_phase_t phase_incr;	/* the phase increment for the next 64 samples */
	fluid_buf_t amp_incr;		/* amplitude increment value */
	fluid_buf_t *dsp_buf;		/* buffer to store interpolated sample data to */

	uint8_t is_looping;
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
